the-ress/prusa-lcd-reader/other/prusa-lcd-reader-rounded-B_Cu.gbr_mt_paint_cnc_adjusted.png

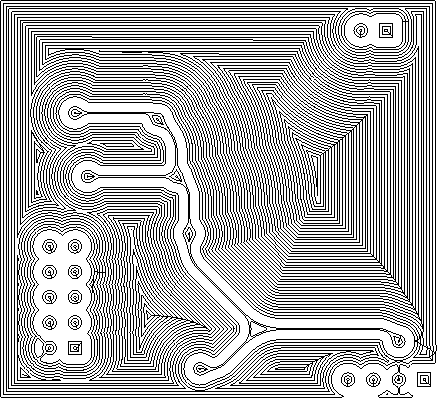
other/prusa-lcd-reader-rounded-B_Cu.gbr_mt_paint_cnc_adjusted.png
